peterzimon/funk-unit-synth/1.1/src/synth.h

#ifndef _SYNTH_H
#define _SYNTH_H

#include "settings.h"
#include "ui.h"
#include "math.h"

#include "hardware/pio.h"
#include "hardware/clocks.h"
#include "hardware/pwm.h"

#include <utils.h>
#include <midi_parser.h>
#include <ringbuffer.h>
#include <adsr.h>
#include <mcp48x2.h>

#include "i_converter.h"
#include "./converters/para.h"
#include "./converters/mono.h"

#define MIDI_BUFFER_SIZE 32
#define MIDDLE_C 60
#define TOP_NOTE 127

// const uint16_t DIV_COUNTER = 1250;

class Synth: public MidiParser {
public:
    static Synth& get_instance() {
        static Synth instance;
        return instance;
    }

    DISALLOW_COPY_AND_ASSIGN(Synth);

    void init(device_mode default_mode);
    void init_dcos();
    void process();

    void note_on(uint8_t channel, uint8_t note, uint8_t velocity);
    void note_off(uint8_t channel, uint8_t note, uint8_t velocity);
    void pitch_bend(uint8_t channel, uint16_t bend);
    void cc(uint8_t channel, uint8_t data1, uint8_t data2);

    // Settings
    void set_mode(device_mode mode);
    void set_solo(bool solo) { settings.solo = solo; }
    void set_detune(bool detune) { settings.detune = detune; }
    void set_portamento(bool portamento) { settings.portamento = portamento; }
    void set_kb_tracking(bool kb_tracking);
    void set_velo_tracking(bool velo_tracking);
    void set_adsr(bool soft, bool hold, bool ring);

    int m_no_of_played_notes = 0;
    int m_notes_played[VOICES];
    volatile int m_chord_notes[VOICES];
    int m_no_of_chord_notes = 0;
    int m_history_records = 0;
    bool m_record_history = true;
    bool m_chord_set = false;
    int m_note_history[VOICES];
    int active_chord_base_note = -1;

    void m_increase_no_of_played_notes();
    void m_decrease_no_of_played_notes();
    void m_remove_played_note(uint8_t note);
    void m_reset_chord_notes();
    void m_reset_note_history();
    void m_set_chord();
    void chord_off();

protected:
    Synth();

private:
    IConverter *m_converter;
    Mono m_mono;
    Para m_para;
    int m_voices = VOICES;

    uint64_t m_attack;
    uint64_t m_decay;
    int m_sustain;
    uint64_t m_release;

    ADSR m_adsr;
    MCP48X2 m_dac;

    uint8_t m_amp_pwm_slices[VOICES];

    bool m_pitch_bend_dirty;
    uint16_t m_midi_pitch_bend = 0x2000;
    uint16_t m_last_midi_pitch_bend = 0x2000;

    uint8_t m_buffer_var[MIDI_BUFFER_SIZE];
    RingBuffer m_input_buffer;

    uint8_t m_modwheel = 0;
    uint8_t m_last_velocity = 0;

    UI &m_ui = UI::get_instance();

    void m_read_midi();
    void m_set_frequency(PIO pio, uint sm, float freq);
    void m_update_dcos(void);
    void m_apply_mods();

    void m_update_envelope();
    void m_update_filter_mod(uint8_t velocity);
    void m_reset_filter_mod();

    float m_pitch_bend_freq(float freq, uint16_t pitch_bend);
};

#endif
