peterzimon/funk-unit-synth/1.1/src/ui.cpp

#include "ui.h"

void UI::init() {
    adc_init();
    adc_gpio_init(ADC_RING_LEN_PIN);
    adc_gpio_init(ADC_SYNTH_MODE_PIN);
    adc_select_input(ADC_RING_LEN_CHANNEL);

    // Binary MUX GPIO setup
    gpio_init(MUX_BINARY_PIN_A);
    gpio_init(MUX_BINARY_PIN_B);
    gpio_init(MUX_BINARY_PIN_C);
    gpio_init(MUX_BINARY_INPUT);

    gpio_set_dir(MUX_BINARY_PIN_A, GPIO_OUT);
    gpio_set_dir(MUX_BINARY_PIN_B, GPIO_OUT);
    gpio_set_dir(MUX_BINARY_PIN_C, GPIO_OUT);
    gpio_set_dir(MUX_BINARY_INPUT, GPIO_IN);

    if (ENABLE_CHORD_MEMORY) {
        gpio_init(BTN_CHORD);
        gpio_set_dir(BTN_CHORD, GPIO_IN);
        gpio_pull_up(BTN_CHORD);
        gpio_init(LED_CHORD);
        gpio_set_dir(LED_CHORD, GPIO_OUT);
    }

    gpio_pull_up(MUX_BINARY_INPUT);

    m_mux_step = 0;
}

void UI::init_scan() {
    for (int i = 0; i < NO_OF_SWITCHES; i++) {
        gpio_put(MUX_BINARY_PIN_A, i & (1 << 0));
        gpio_put(MUX_BINARY_PIN_B, i & (1 << 1));
        gpio_put(MUX_BINARY_PIN_C, i & (1 << 2));
        bool sw_read = !gpio_get(MUX_BINARY_INPUT);
        switches[static_cast<mux_switch>(i)] = false;
    }

    adc_select_input(ADC_RING_LEN_CHANNEL);
    release_long = adc_read();

    adc_select_input(ADC_SYNTH_MODE_CHANNEL);
    release_long = adc_read();
}

void UI::scan() {
    // Read switches (muxed). The CD4051 needs some time to settle after setting
    // the input address (X0...X7). This is a simple way to add a little delay
    // to the whole scan cycle. Also note that it only works reliably if the
    // delay is in between reading the input and setting the address. That's why
    // here the address is only set after reading the input for the next cycle.
    if (m_scan_cycle < SCAN_CYCLE) {
        m_scan_cycle++;
        updated = false;
        return;
    }

    bool switch_value = !gpio_get(MUX_BINARY_INPUT);
    mux_switch current_switch = static_cast<mux_switch>(m_mux_step);
    switches[current_switch] = switch_value;

    m_mux_step++;

    gpio_put(MUX_BINARY_PIN_A, m_mux_step & (1 << 0));
    gpio_put(MUX_BINARY_PIN_B, m_mux_step & (1 << 1));
    gpio_put(MUX_BINARY_PIN_C, m_mux_step & (1 << 2));

    m_mux_step &= 0x7; // Reset to 0 after 8 steps
    m_scan_cycle = 0;

    // Read ADC
    adc_select_input(ADC_RING_LEN_CHANNEL);
    uint16_t adc_read_value = adc_read();

    decay_long = Utils::map(adc_read_value >> 4, 0, 256, DECAY_LONG_MIN, DECAY_LONG_MAX);
    release_long = Utils::map(adc_read_value >> 4, 0, 256, RELEASE_LONG_MIN, RELEASE_LONG_MAX);

    adc_select_input(ADC_SYNTH_MODE_CHANNEL);

    synth_mode = static_cast<device_mode>(Utils::map(adc_read(), 0, 4096, 0, NO_OF_MODES));

    updated = true;

    // Read chord button
    if (ENABLE_CHORD_MEMORY) {
        bool chord_is_pushed = !gpio_get(BTN_CHORD);

        if (chord_is_pushed && !m_btn_chord_pushed) {
            m_t_chord_pushed = Utils::millis();
            m_btn_chord_pushed = true;
        }

        // Not a long press
        if (m_btn_chord_pushed && !chord_is_pushed) {
            uint32_t pushtime = Utils::millis() - m_t_chord_pushed;
            if (pushtime > 50 && pushtime < LONG_PRESS_MILLIS) {
                chord_on = !chord_on;
            }
            m_btn_chord_pushed = false;

        // Keep on pushing...
        } else if (chord_is_pushed && chord_on) {
            uint32_t pushtime = Utils::millis() - m_t_chord_pushed;
            if (pushtime >= LONG_PRESS_MILLIS) {
                chord_on = false;
                reset_chord = true;
            }
        }

        gpio_put(LED_CHORD, chord_on);
    }

    // debug();
}

void UI::debug() {
    printf("Binary inputs:\n");
    for (int i = 0; i < NO_OF_SWITCHES; i++) {
        printf("%d: %d\n", i, (int)switches[static_cast<mux_switch>(i)]);
    }
    printf("Ring length: %lu\n", release_long);
    printf("Synth mode: %d\n", synth_mode);
    printf("\n");
}
