peterzimon/funk-unit-synth/1.1/src/ui.h

#ifndef _UI_H
#define _UI_H

#include <stdio.h>
#include <math.h>
#include <utils.h>
#include <map>
#include <pico/stdio.h>
#include "hardware/adc.h"
#include "hardware/gpio.h"
#include "settings.h"
#include <button.h>

// The UI doesn't have to be scanned in every processor cycle. To save processor
// time define the number cycles for which the UI should not be scanned.
#define SCAN_CYCLE 100
#define LONG_PRESS_MILLIS 1000

class UI {
public:
    static UI& get_instance() {
        static UI instance;
        return instance;
    }

    DISALLOW_COPY_AND_ASSIGN(UI);

    std::map<mux_switch, bool> switches;
    device_mode synth_mode = device_mode::MONO;
    uint16_t release_long = RELEASE_LONG_MIN;
    uint16_t decay_long = DECAY_LONG_MIN;
    bool updated = true;
    bool chord_on = false;
    bool reset_chord = false;

    void init();
    void init_scan();
    void scan();

protected:
    UI() = default;

private:
    uint16_t m_mux_step = 0;
    int m_scan_cycle = 0;

    bool m_btn_chord_pushed = false;
    uint32_t m_t_chord_pushed = 0;

    void debug();
};

#endif
